jp112sdl/HB-UNI-Sen-WEA/3DDruck/LTB_Weather_Station/images/0f729904a5f2e05334bc5dd88b66ae25_preview_featured.jpg

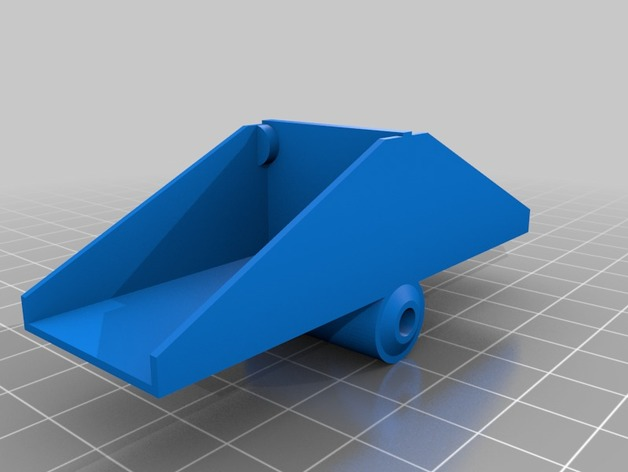
3DDruck/LTB_Weather_Station/images/0f729904a5f2e05334bc5dd88b66ae25_preview_featured.jpg
