jp112sdl/HB-UNI-Sen-WEA/3DDruck/LTB_Weather_Station/images/2f4eb67d5eb4e4a115d83a93fdd548bd_preview_featured.jpg

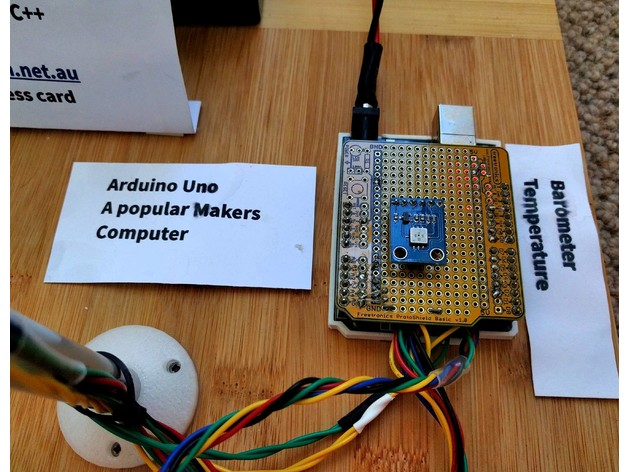
3DDruck/LTB_Weather_Station/images/2f4eb67d5eb4e4a115d83a93fdd548bd_preview_featured.jpg
