jp112sdl/HB-UNI-Sen-WEA/3DDruck/LTB_Weather_Station/images/3d7bd073ae92bd9a4f123ed83592e2da_preview_featured.jpg

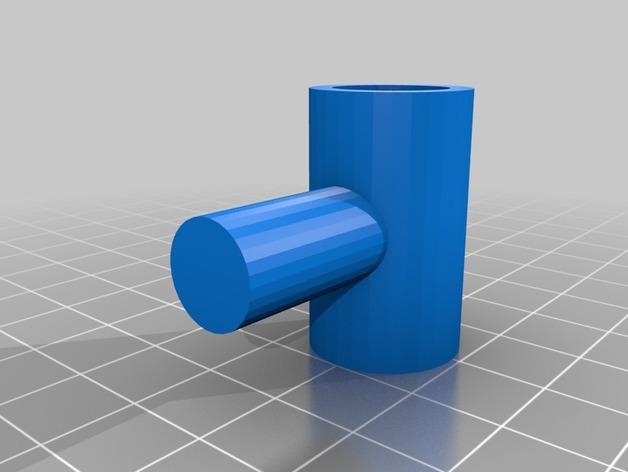
3DDruck/LTB_Weather_Station/images/3d7bd073ae92bd9a4f123ed83592e2da_preview_featured.jpg
