jp112sdl/HB-UNI-Sen-WEA/3DDruck/LTB_Weather_Station/images/6b7efd5bf7d866a3c7be1622005885e2_preview_featured.jpg

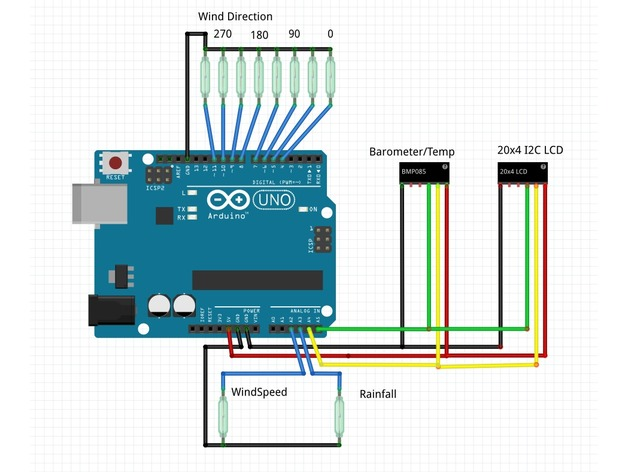
3DDruck/LTB_Weather_Station/images/6b7efd5bf7d866a3c7be1622005885e2_preview_featured.jpg
