jp112sdl/HB-UNI-Sen-WEA/3DDruck/LTB_Weather_Station/images/6f4c261a202a8efb6d09fc4429fcd451_preview_featured.jpg

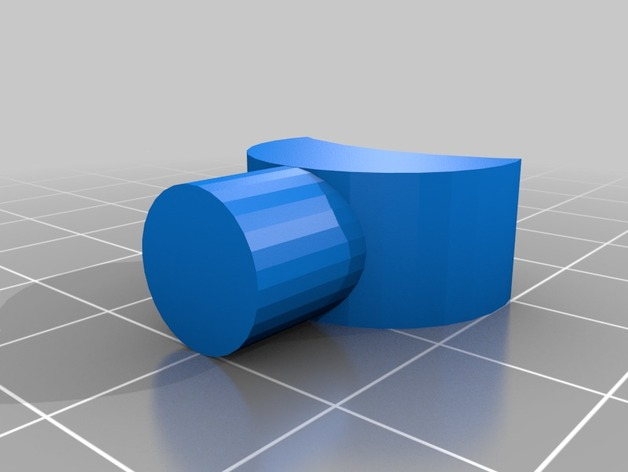
3DDruck/LTB_Weather_Station/images/6f4c261a202a8efb6d09fc4429fcd451_preview_featured.jpg
