jp112sdl/HB-UNI-Sen-WEA/3DDruck/LTB_Weather_Station/images/6f54eee4d5941a1848efe295c70625fb_preview_featured.jpg

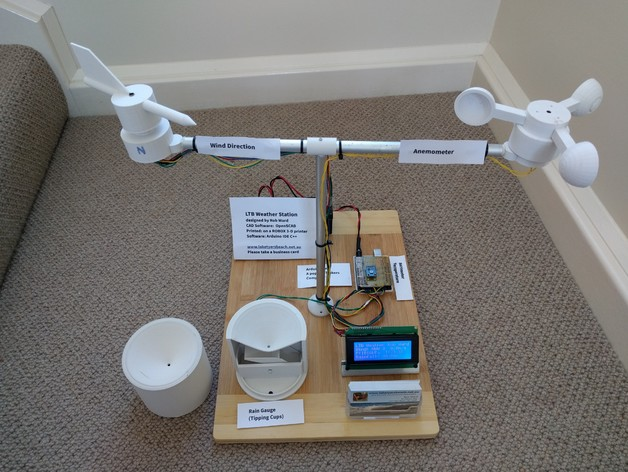
3DDruck/LTB_Weather_Station/images/6f54eee4d5941a1848efe295c70625fb_preview_featured.jpg
