jp112sdl/HB-UNI-Sen-WEA/3DDruck/LTB_Weather_Station/images/7dec8525ebd62560725952abd26e961d_preview_featured.jpg

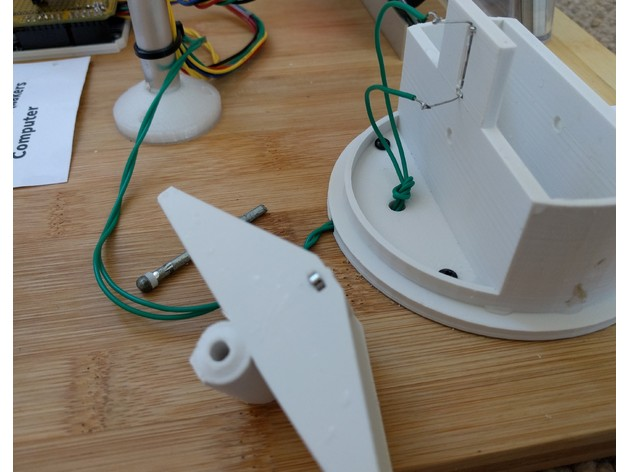
3DDruck/LTB_Weather_Station/images/7dec8525ebd62560725952abd26e961d_preview_featured.jpg
