jp112sdl/HB-UNI-Sen-WEA/3DDruck/LTB_Weather_Station/images/8c24a9ce323ae254777e71005f5087d5_preview_featured.jpg

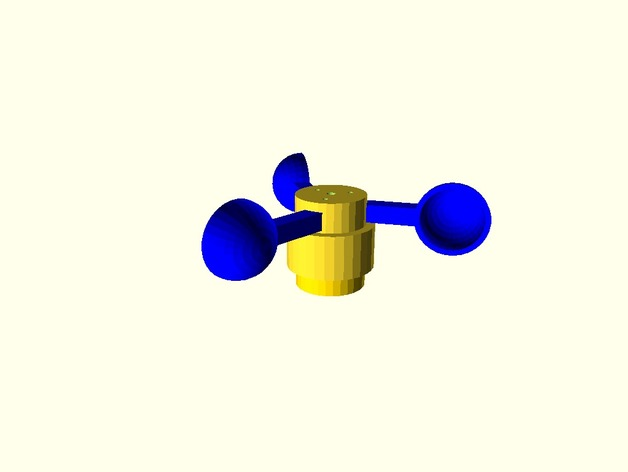
3DDruck/LTB_Weather_Station/images/8c24a9ce323ae254777e71005f5087d5_preview_featured.jpg
