jp112sdl/HB-UNI-Sen-WEA/3DDruck/LTB_Weather_Station/images/45c1245175a171400667a6d880b7b2a3_preview_featured.jpg

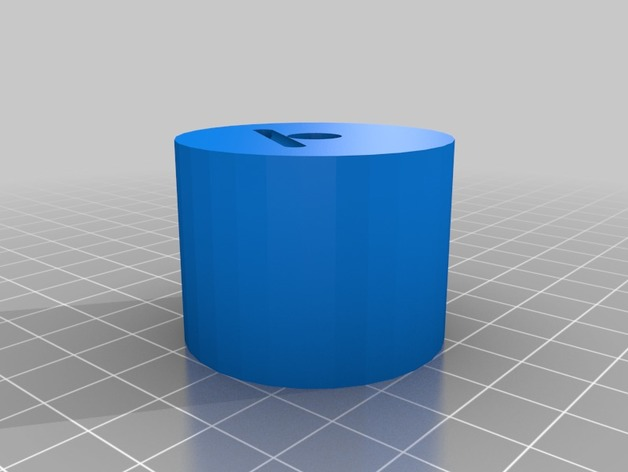
3DDruck/LTB_Weather_Station/images/45c1245175a171400667a6d880b7b2a3_preview_featured.jpg
