jp112sdl/HB-UNI-Sen-WEA/3DDruck/LTB_Weather_Station/images/80a48253a995d0b735cc264a9117a01e_preview_featured.jpg

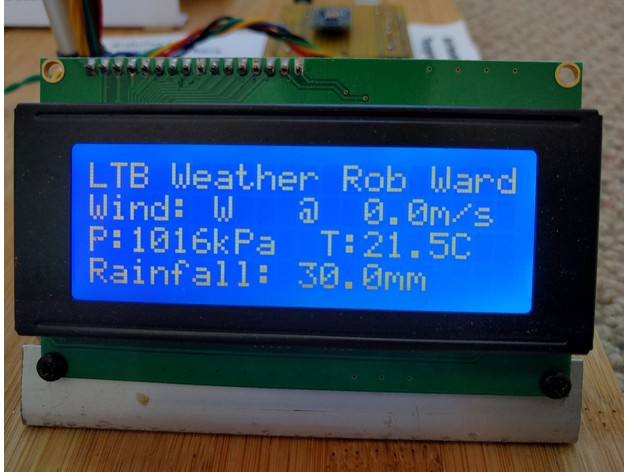
3DDruck/LTB_Weather_Station/images/80a48253a995d0b735cc264a9117a01e_preview_featured.jpg
