jp112sdl/HB-UNI-Sen-WEA/3DDruck/LTB_Weather_Station/images/665cde6034edafd1919697d14e3cbb7f_preview_featured.jpg

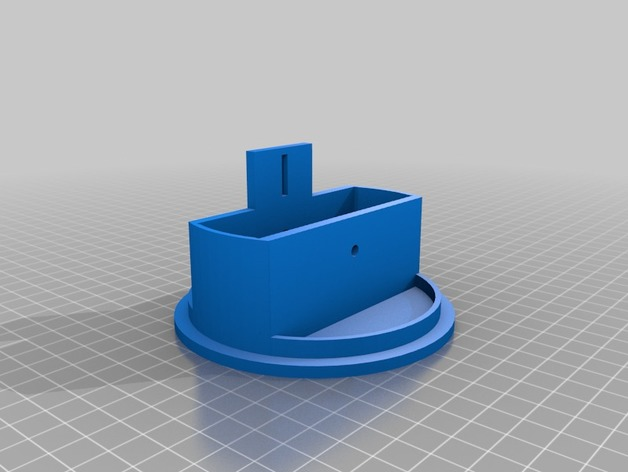
3DDruck/LTB_Weather_Station/images/665cde6034edafd1919697d14e3cbb7f_preview_featured.jpg
