jp112sdl/HB-UNI-Sen-WEA/3DDruck/LTB_Weather_Station/images/4128c8499053c0b8ed6bece59226a6e4_preview_featured.jpg

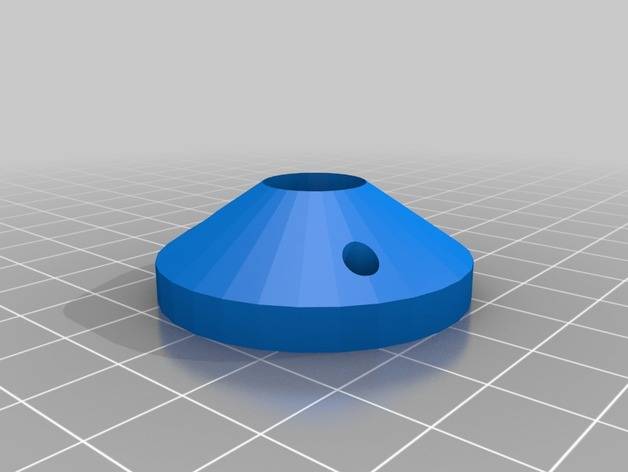
3DDruck/LTB_Weather_Station/images/4128c8499053c0b8ed6bece59226a6e4_preview_featured.jpg
