jp112sdl/HB-UNI-Sen-WEA/3DDruck/LTB_Weather_Station/images/7844c83e0afc9eee98446c4f50ffa83b_preview_featured.jpg

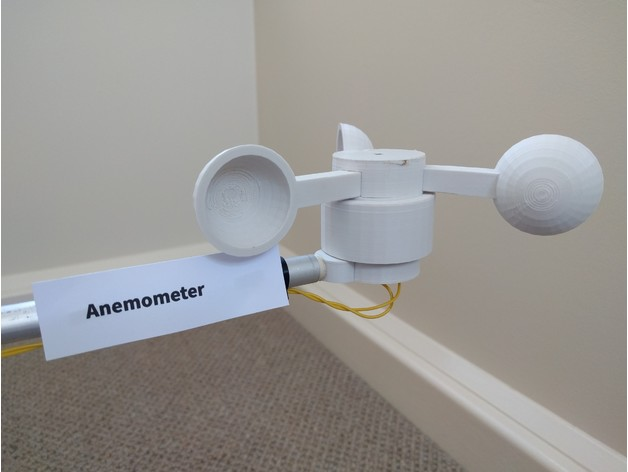
3DDruck/LTB_Weather_Station/images/7844c83e0afc9eee98446c4f50ffa83b_preview_featured.jpg
