jp112sdl/HB-UNI-Sen-WEA/3DDruck/LTB_Weather_Station/images/9245b32cea09aa1bce04a988e750eaf5_preview_featured.jpg

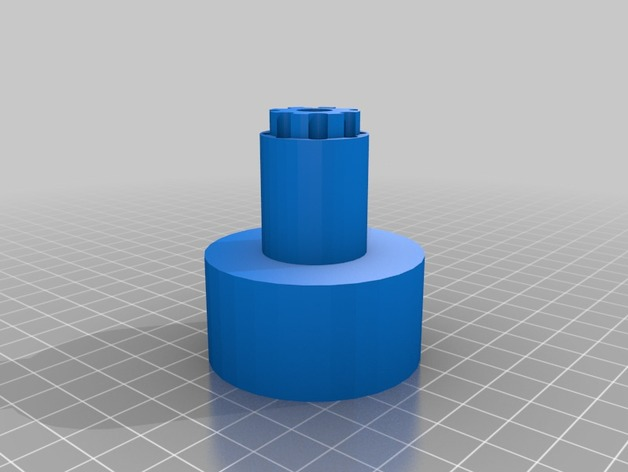
3DDruck/LTB_Weather_Station/images/9245b32cea09aa1bce04a988e750eaf5_preview_featured.jpg
