jp112sdl/HB-UNI-Sen-WEA/3DDruck/LTB_Weather_Station/images/15661ac53241d97e30403f3ccd07a3a0_preview_featured.jpg

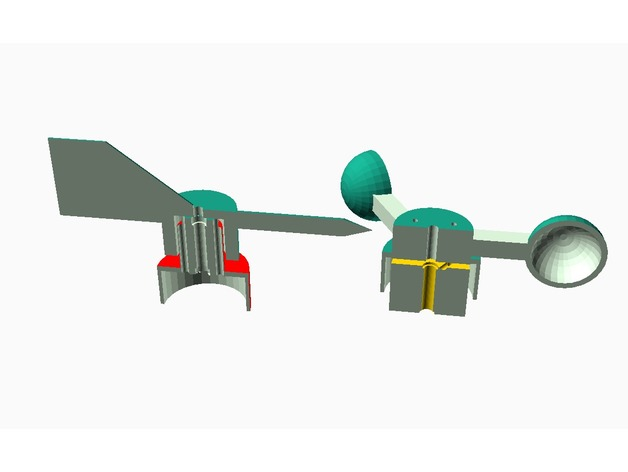
3DDruck/LTB_Weather_Station/images/15661ac53241d97e30403f3ccd07a3a0_preview_featured.jpg
