jp112sdl/HB-UNI-Sen-WEA/3DDruck/LTB_Weather_Station/images/a46b4e9dc1ee91424486a30a58d59f65_preview_featured.jpg

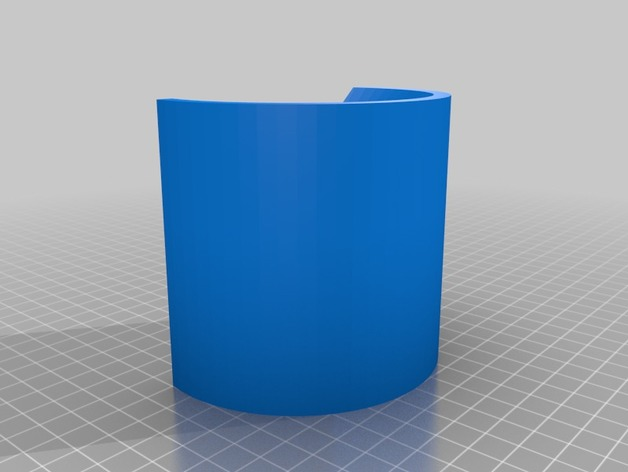
3DDruck/LTB_Weather_Station/images/a46b4e9dc1ee91424486a30a58d59f65_preview_featured.jpg
