jp112sdl/HB-UNI-Sen-WEA/3DDruck/LTB_Weather_Station/images/aa5c15dc5b5677d0f9d4d23d35d61b8d_preview_featured.jpg

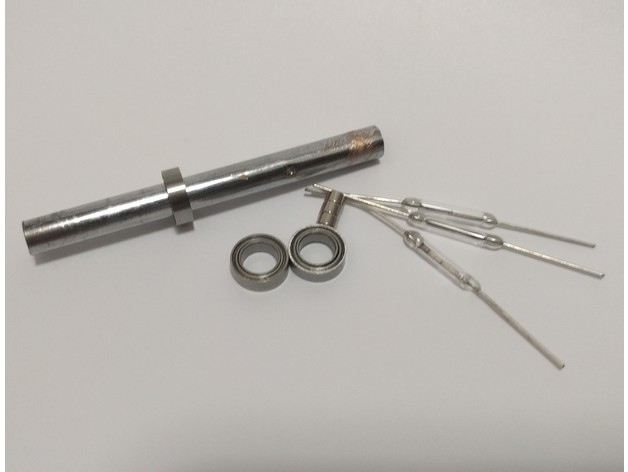
3DDruck/LTB_Weather_Station/images/aa5c15dc5b5677d0f9d4d23d35d61b8d_preview_featured.jpg
