jp112sdl/HB-UNI-Sen-WEA/3DDruck/LTB_Weather_Station/images/abda42896f2a54828468f4c982fa79e0_preview_featured.jpg

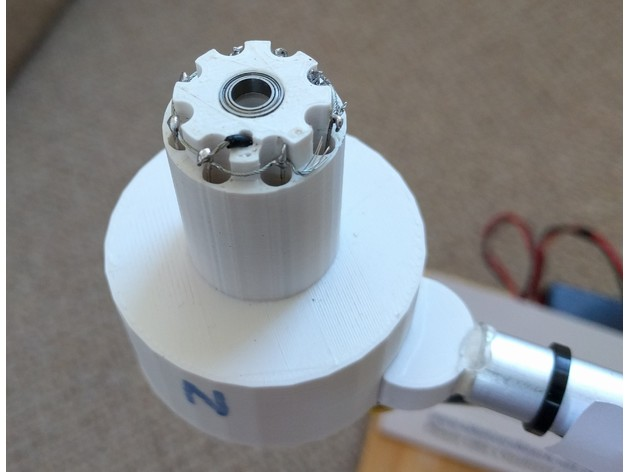
3DDruck/LTB_Weather_Station/images/abda42896f2a54828468f4c982fa79e0_preview_featured.jpg
