jp112sdl/HB-UNI-Sen-WEA/3DDruck/LTB_Weather_Station/images/b8ac2ffeab8d6cb9135d3699e298f246_preview_featured.jpg

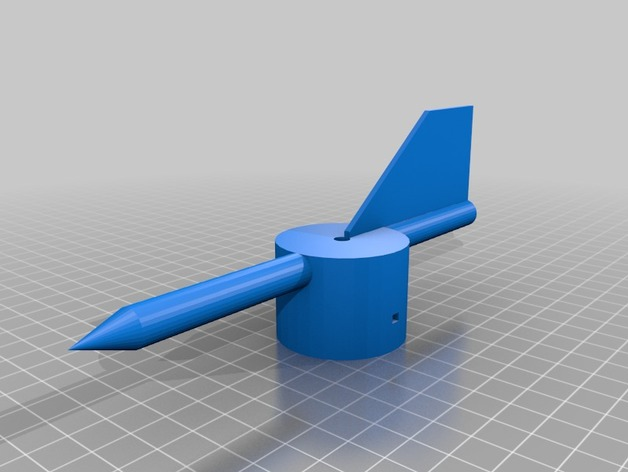
3DDruck/LTB_Weather_Station/images/b8ac2ffeab8d6cb9135d3699e298f246_preview_featured.jpg
