jp112sdl/HB-UNI-Sen-WEA/3DDruck/LTB_Weather_Station/images/c9b82732129711d131ec30678b11e9f1_preview_featured.jpg

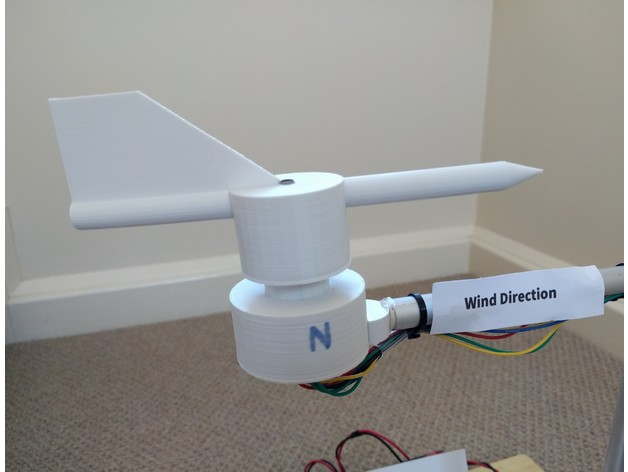
3DDruck/LTB_Weather_Station/images/c9b82732129711d131ec30678b11e9f1_preview_featured.jpg
