jp112sdl/HB-UNI-Sen-WEA/3DDruck/LTB_Weather_Station/images/e383737310d1c1f831bcede16474fa9f_preview_featured.jpg

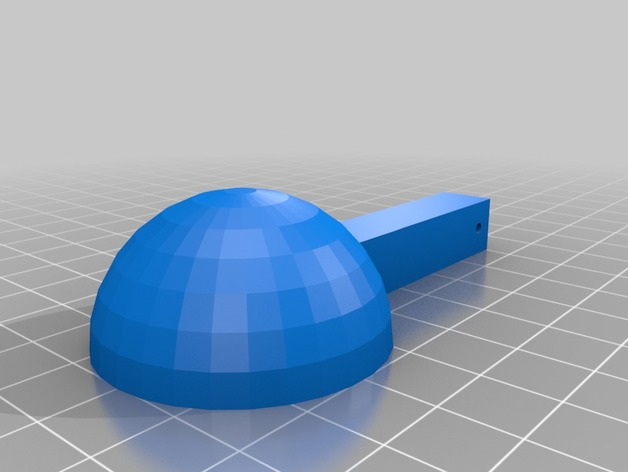
3DDruck/LTB_Weather_Station/images/e383737310d1c1f831bcede16474fa9f_preview_featured.jpg
