jp112sdl/HB-UNI-Sen-WEA/3DDruck/LTB_Weather_Station/images/ef46951516978715a64110eb92978627_preview_featured.jpg

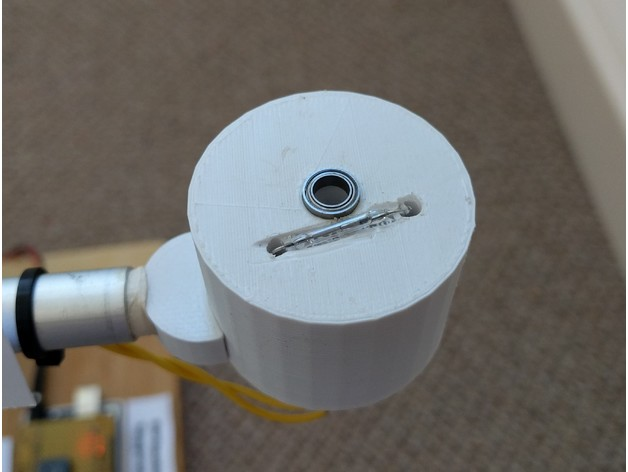
3DDruck/LTB_Weather_Station/images/ef46951516978715a64110eb92978627_preview_featured.jpg
