jp112sdl/HB-UNI-Sen-WEA/3DDruck/LTB_Weather_Station/images/f5733b1c9a6c24a76b0aa705a5f0eb99_preview_featured.jpg

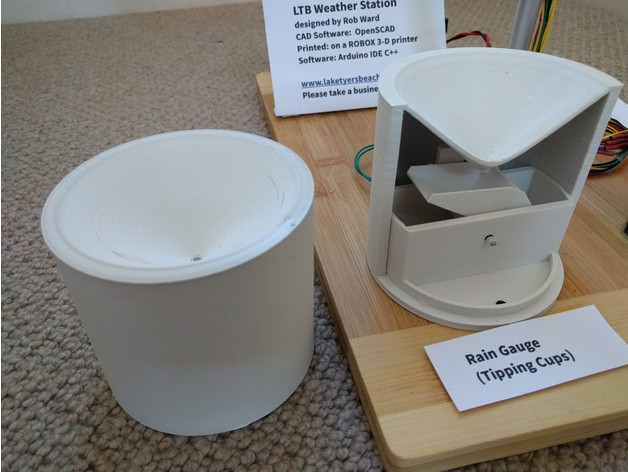
3DDruck/LTB_Weather_Station/images/f5733b1c9a6c24a76b0aa705a5f0eb99_preview_featured.jpg
