jp112sdl/HB-UNI-Sen-WEA/3DDruck/Luftdaten_Stevensson_screen/images/4de7b6a64d3845ae190a4616e7cf8708_preview_featured.jpg

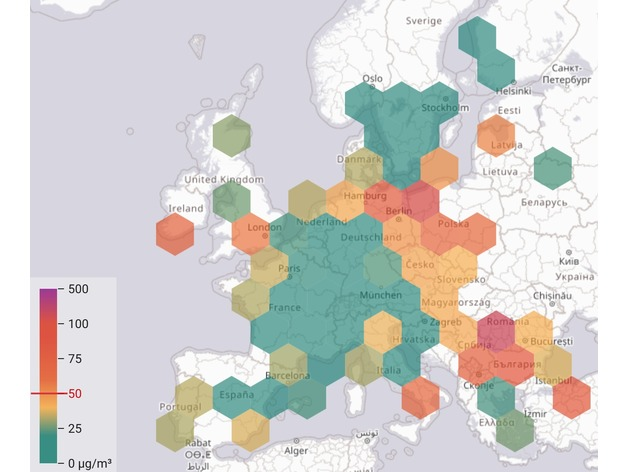
3DDruck/Luftdaten_Stevensson_screen/images/4de7b6a64d3845ae190a4616e7cf8708_preview_featured.jpg
