jp112sdl/HB-UNI-Sen-WEA/3DDruck/Luftdaten_Stevensson_screen/images/44aee935f5d444104dc200fb56da6abe_preview_featured.jpg

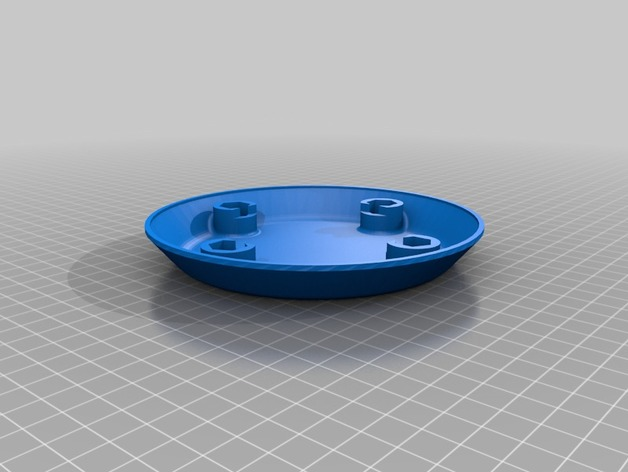
3DDruck/Luftdaten_Stevensson_screen/images/44aee935f5d444104dc200fb56da6abe_preview_featured.jpg
