jp112sdl/HB-UNI-Sen-WEA/3DDruck/Luftdaten_Stevensson_screen/images/160ce06f31e4f0b9b2863523b1d578d7_preview_featured.jpg

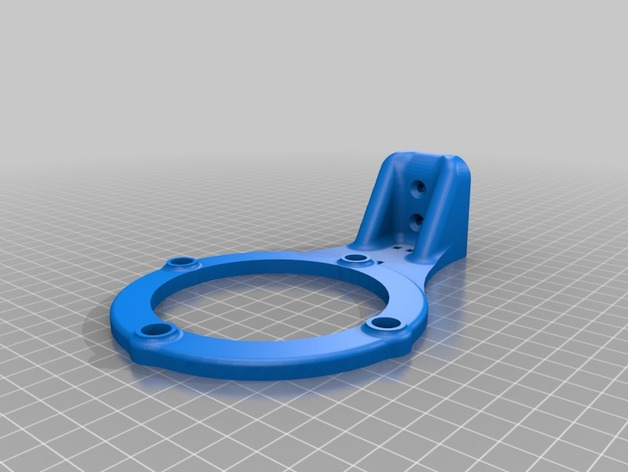
3DDruck/Luftdaten_Stevensson_screen/images/160ce06f31e4f0b9b2863523b1d578d7_preview_featured.jpg
