jp112sdl/HB-UNI-Sen-WEA/3DDruck/Luftdaten_Stevensson_screen/images/da4376fd09404e2d7904c5d9ae312a6a_preview_featured.jpg

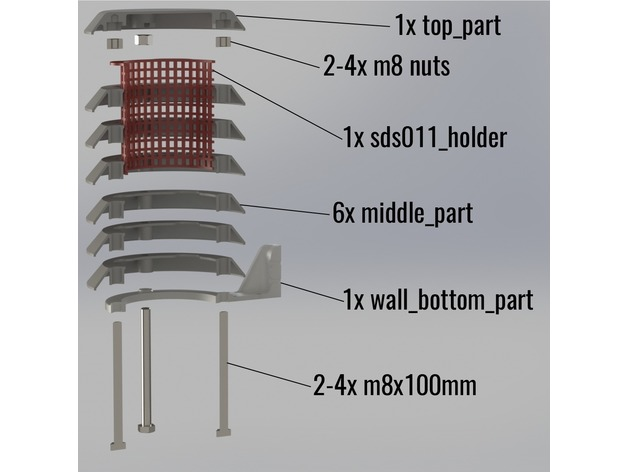
3DDruck/Luftdaten_Stevensson_screen/images/da4376fd09404e2d7904c5d9ae312a6a_preview_featured.jpg
