jp112sdl/HB-UNI-Sen-WEA/Images/0.JPG

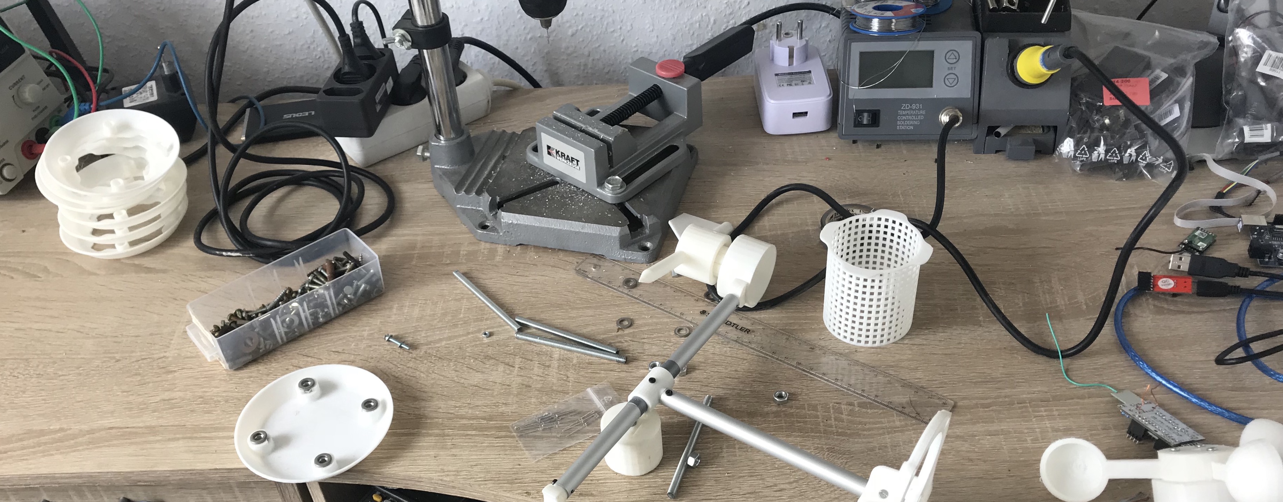
Images/0.JPG
