jp112sdl/HB-UNI-Sen-WEA/Images/1.JPG

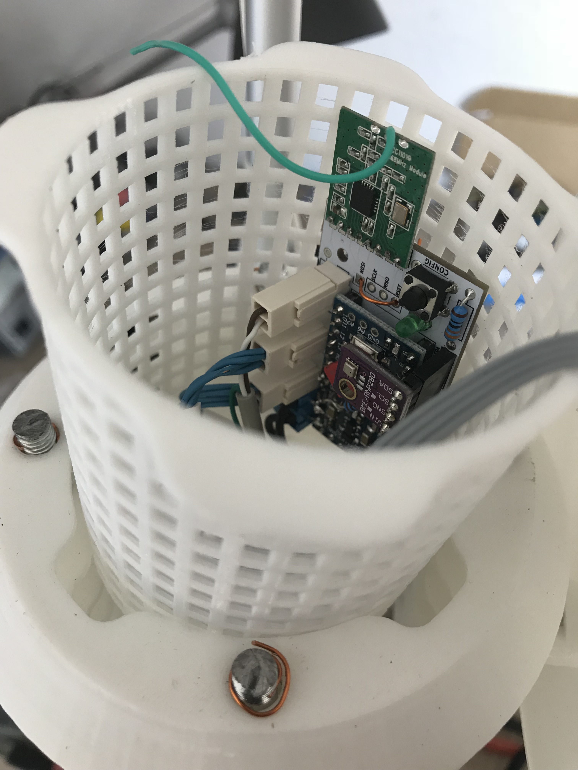
Images/1.JPG
