jp112sdl/HB-UNI-Sen-WEA/Images/2.JPG

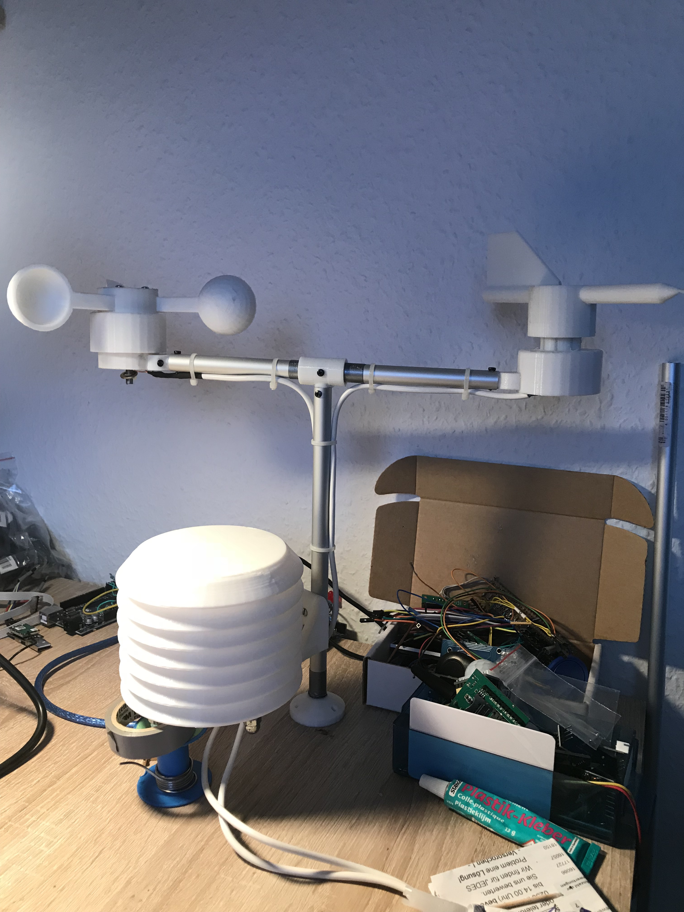
Images/2.JPG
