jp112sdl/HB-UNI-Sen-WEA/Images/3.JPG

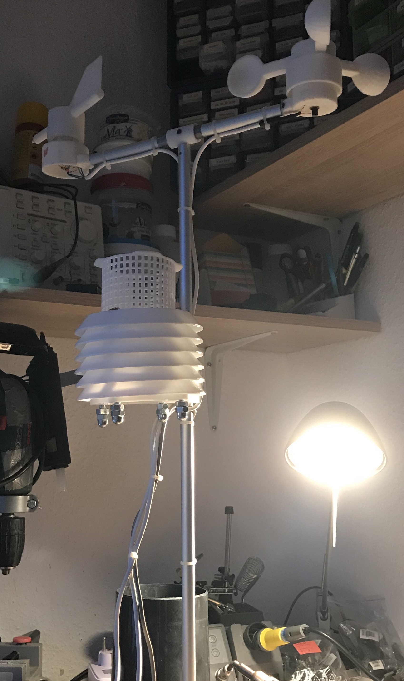
Images/3.JPG
