jp112sdl/HB-UNI-Sen-WEA/Images/Arduino_Boardverwaltung.png

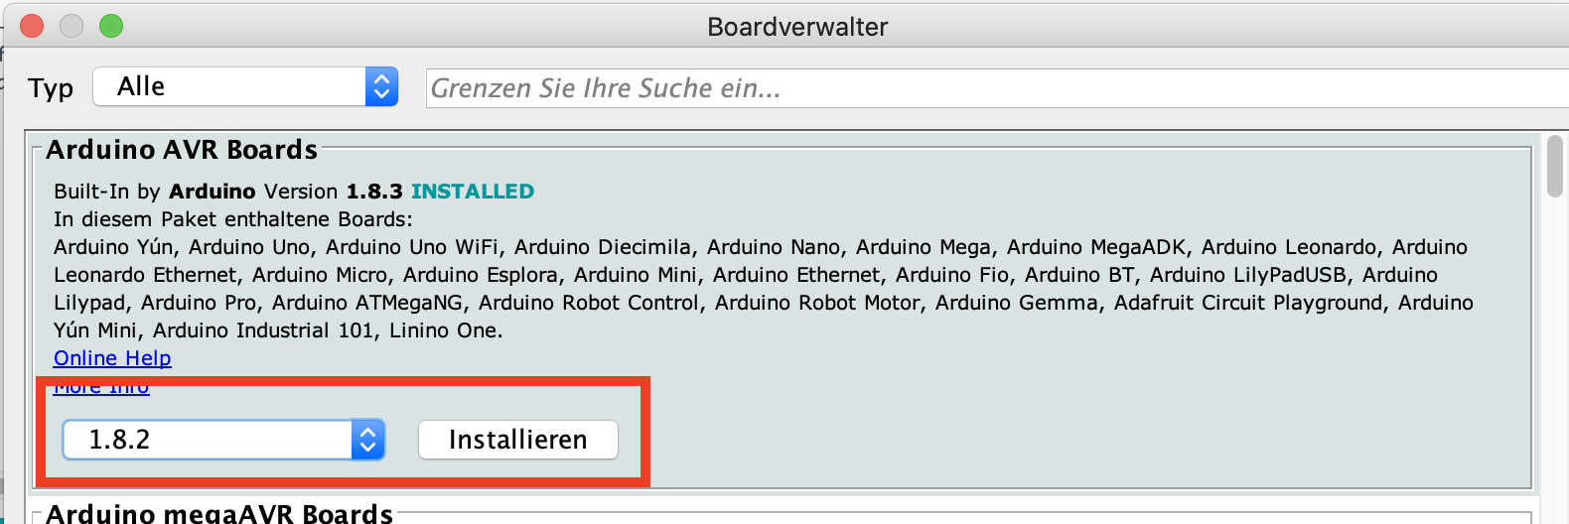
Images/Arduino_Boardverwaltung.png
