jp112sdl/HB-UNI-Sen-WEA/Images/as3935_back_rot.png

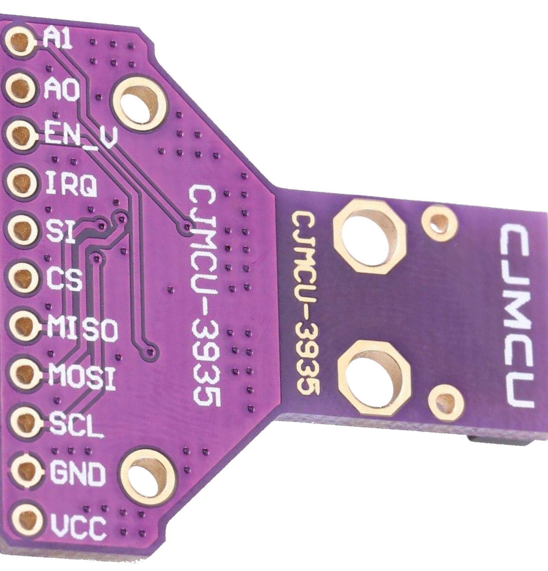
Images/as3935_back_rot.png
