jp112sdl/HB-UNI-Sen-WEA/Images/BME_PFTE.jpeg

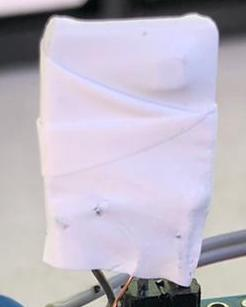
Images/BME_PFTE.jpeg
