jp112sdl/HB-UNI-Sen-WEA/Images/CCU_Addon.png

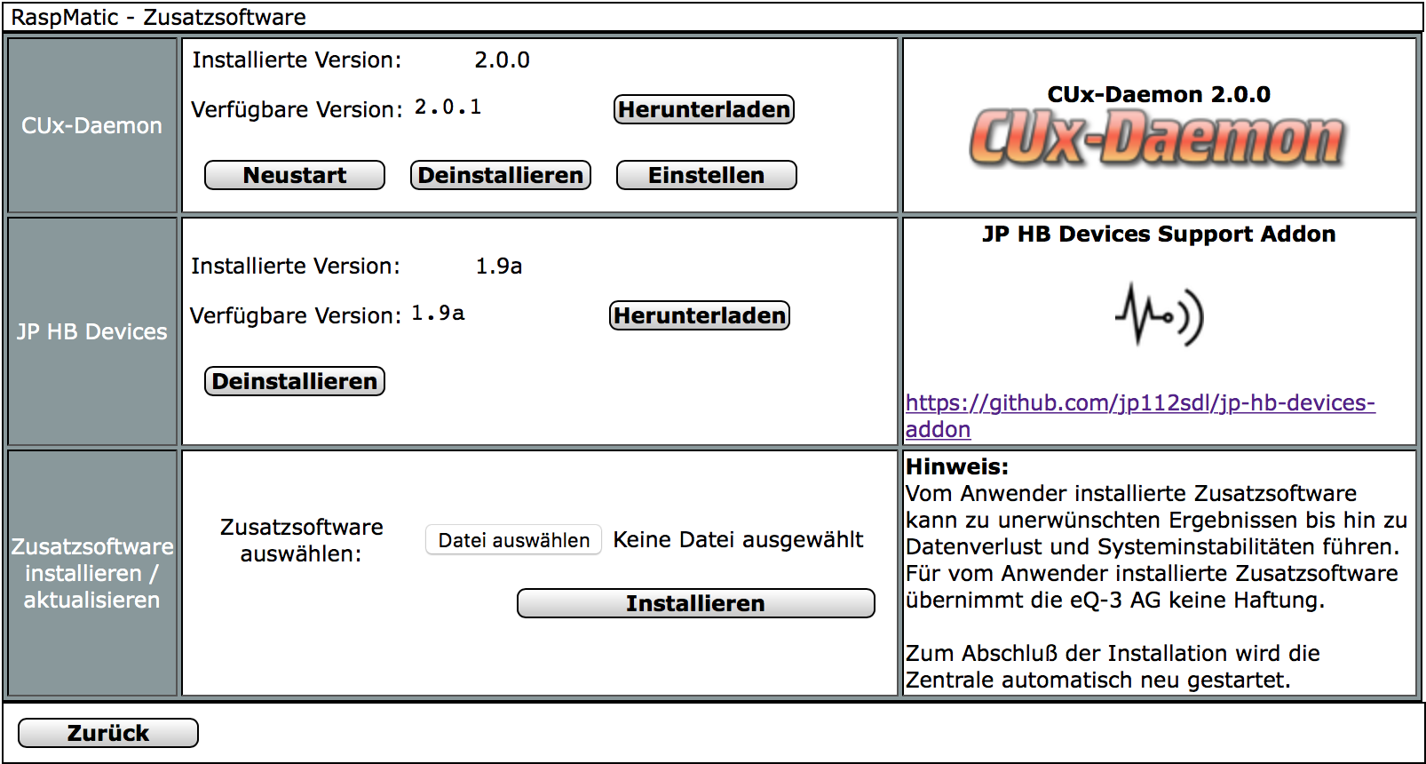
Images/CCU_Addon.png
