jp112sdl/HB-UNI-Sen-WEA/Images/CCU_DV_Regen.png

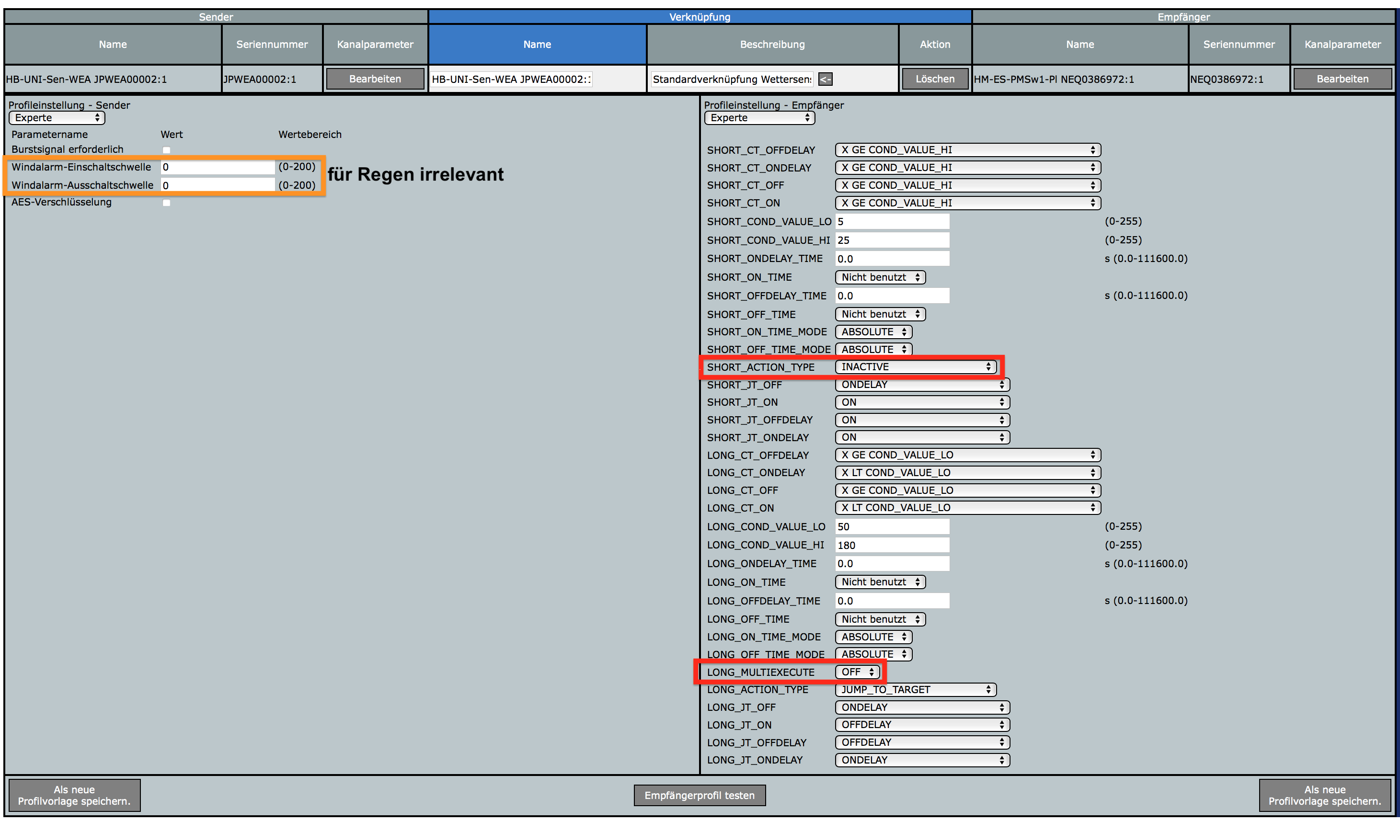
Images/CCU_DV_Regen.png
