jp112sdl/HB-UNI-Sen-WEA/Images/CCU_DV_Sturm.png

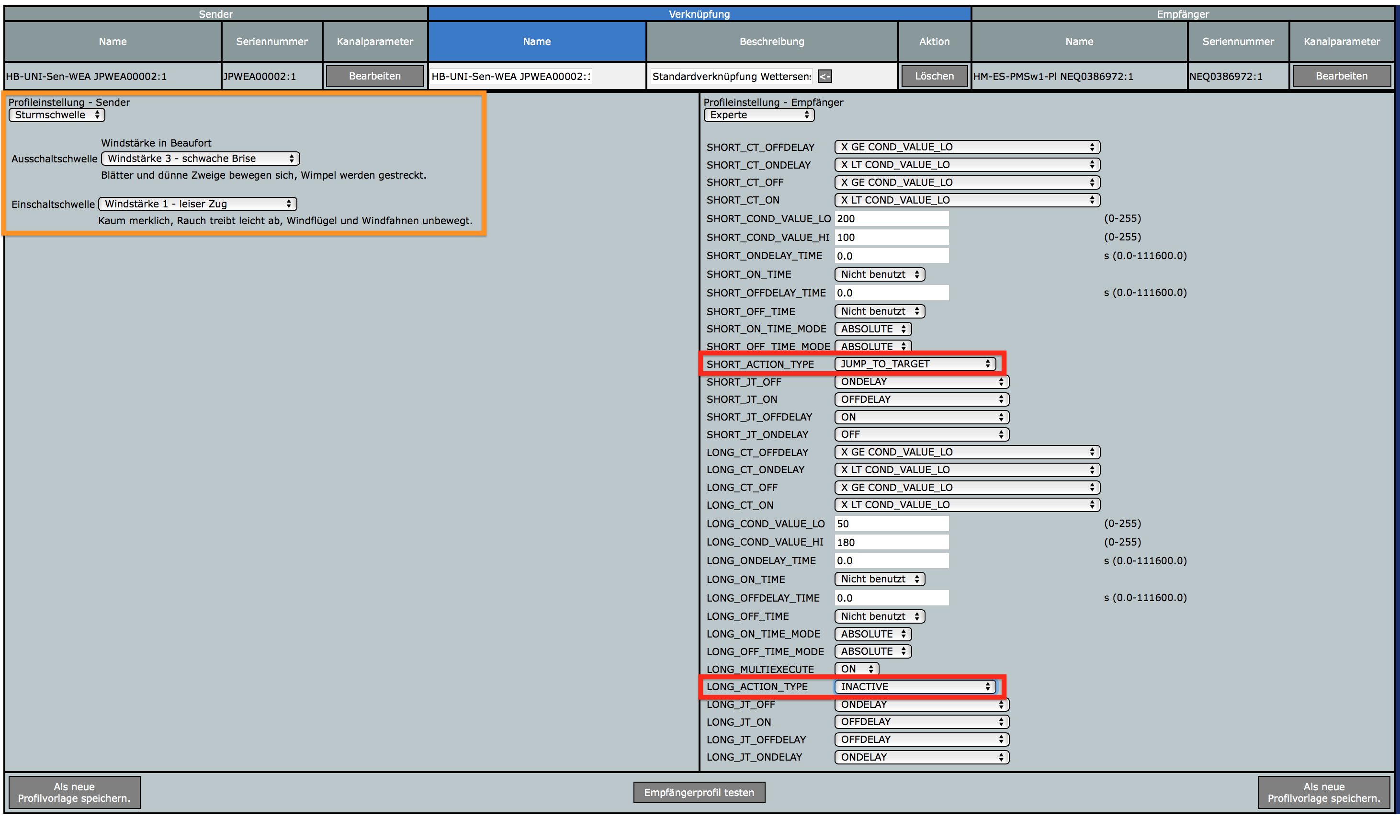
Images/CCU_DV_Sturm.png
