jp112sdl/HB-UNI-Sen-WEA/Images/CCU_Experteneinstellungen.png

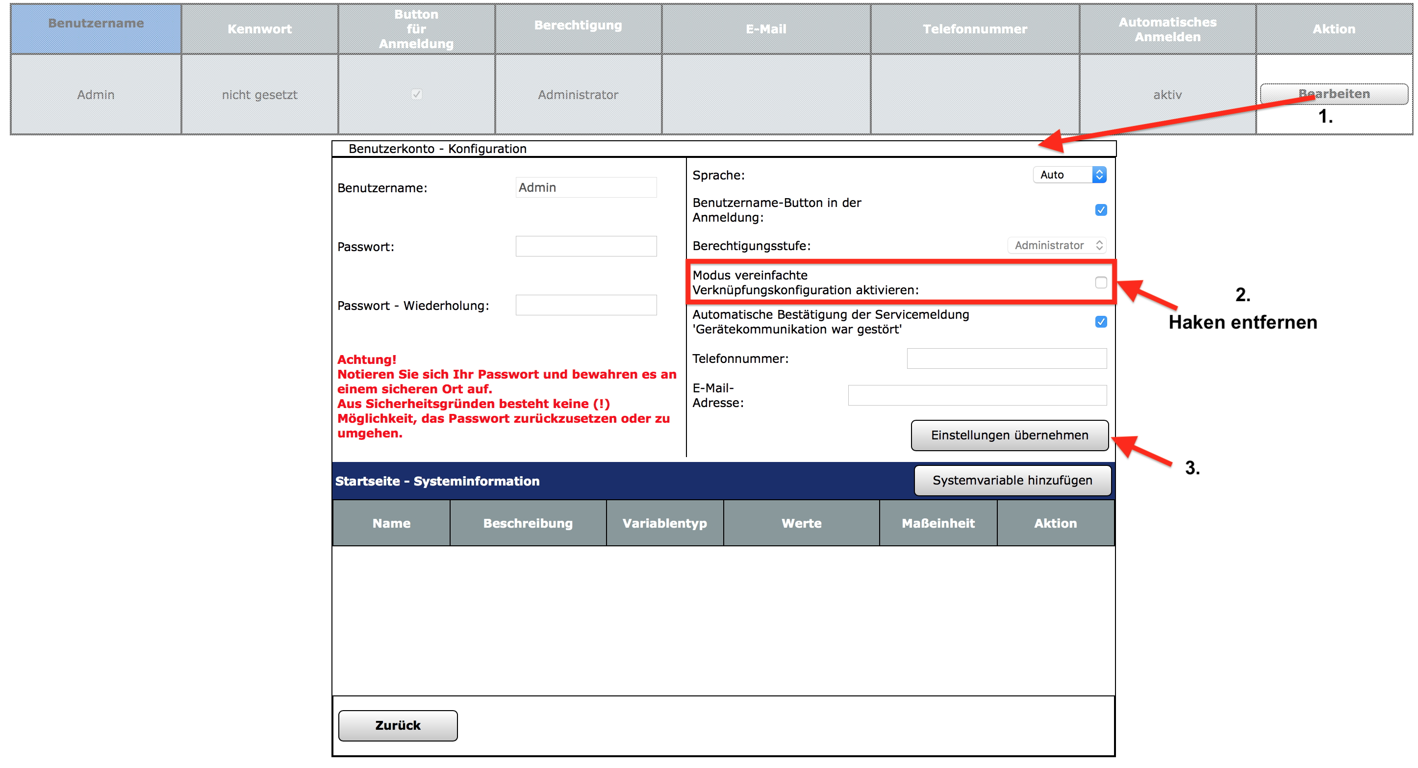
Images/CCU_Experteneinstellungen.png
