jp112sdl/HB-UNI-Sen-WEA/Images/CCU_Geraet.png

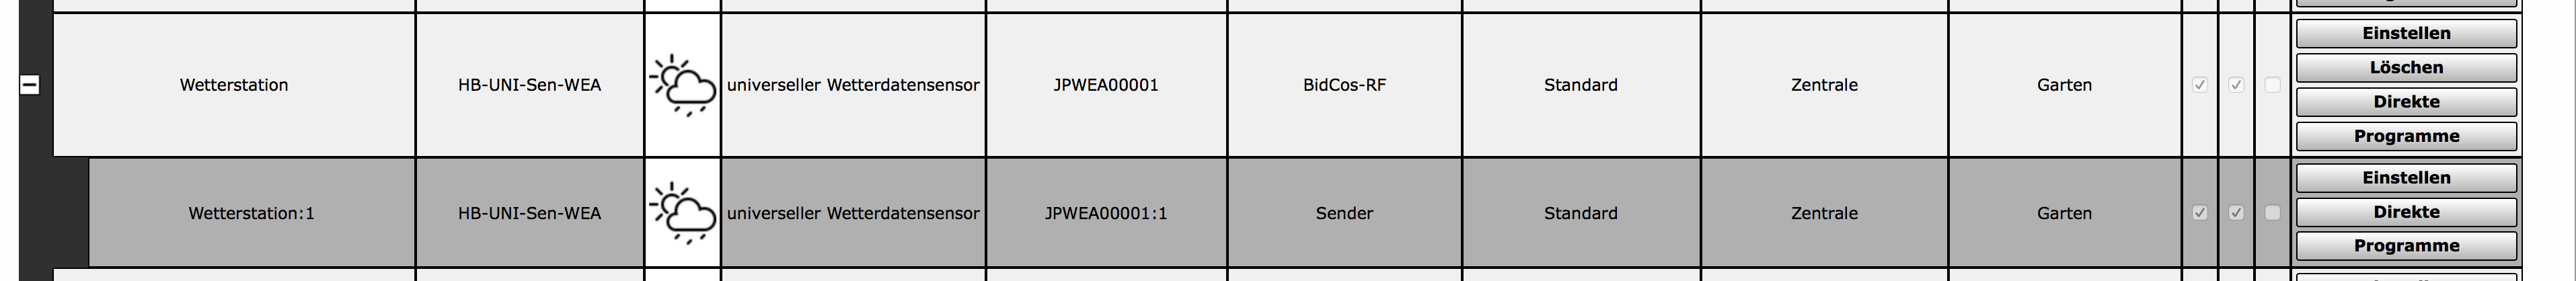
Images/CCU_Geraet.png
