jp112sdl/HB-UNI-Sen-WEA/Images/Connect_AS3935.jpeg

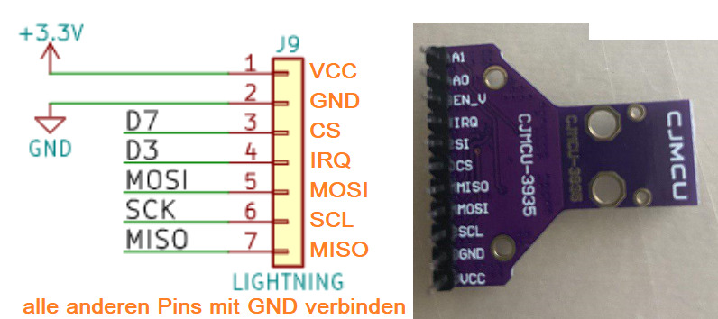
Images/Connect_AS3935.jpeg
