jp112sdl/HB-UNI-Sen-WEA/Images/PCB_Connectors.jpeg

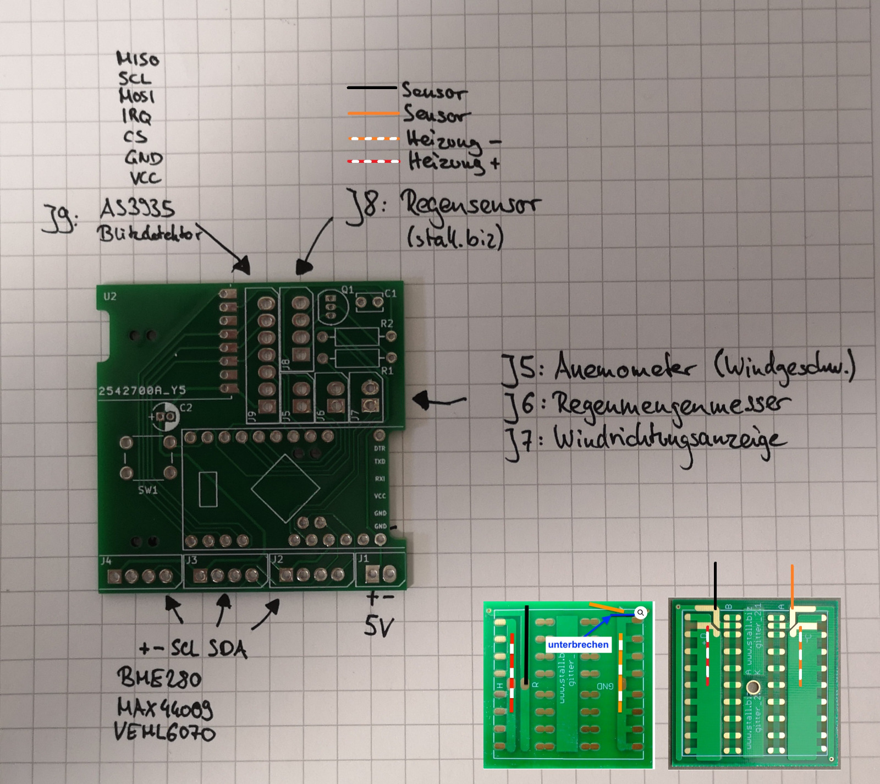
Images/PCB_Connectors.jpeg
