jp112sdl/HB-UNI-Sen-WEA/Images/Platine_bestueckt.jpg

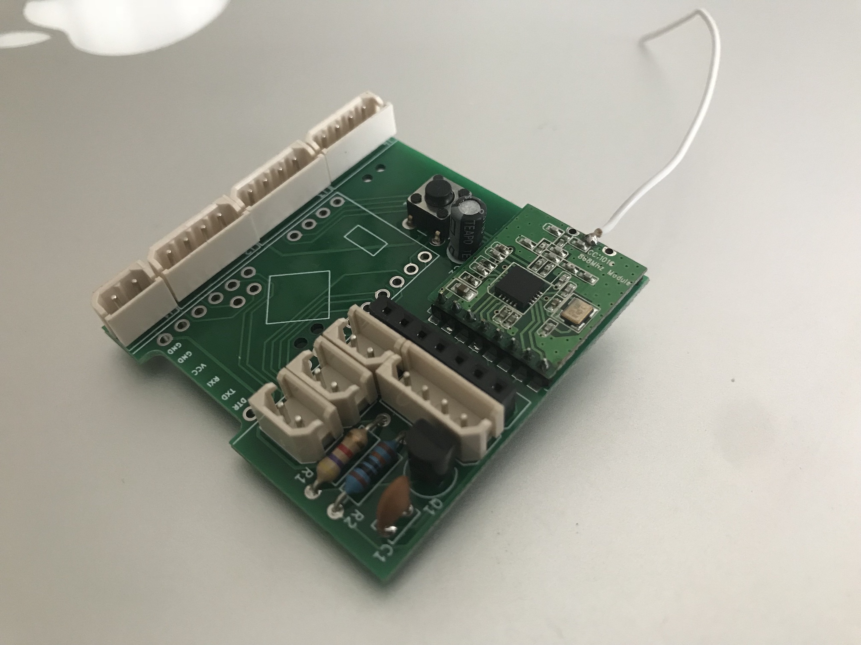
Images/Platine_bestueckt.jpg
