jp112sdl/HB-UNI-Sen-WEA/Images/sample1_2.jpg

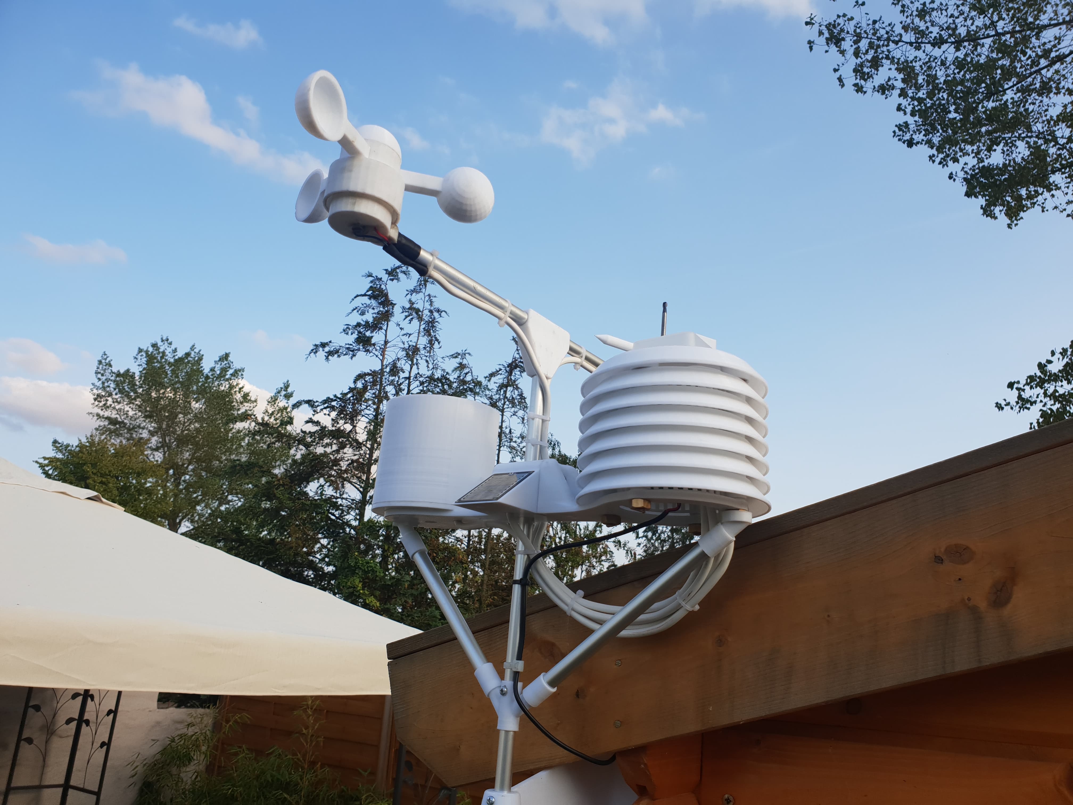
Images/sample1_2.jpg
