jp112sdl/HB-UNI-Sen-WEA/Images/sample1_3.jpg

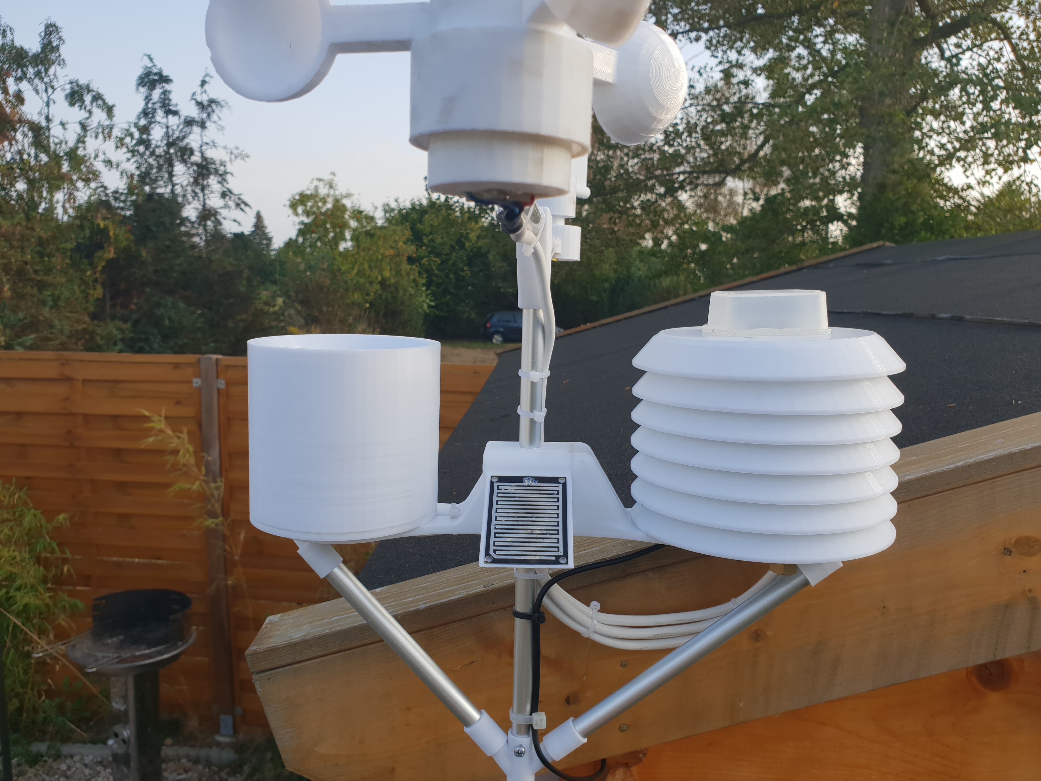
Images/sample1_3.jpg
