jp112sdl/HB-UNI-Sen-WEA/Renkforce_WindVane/2016-11-12-21.50.05.jpg

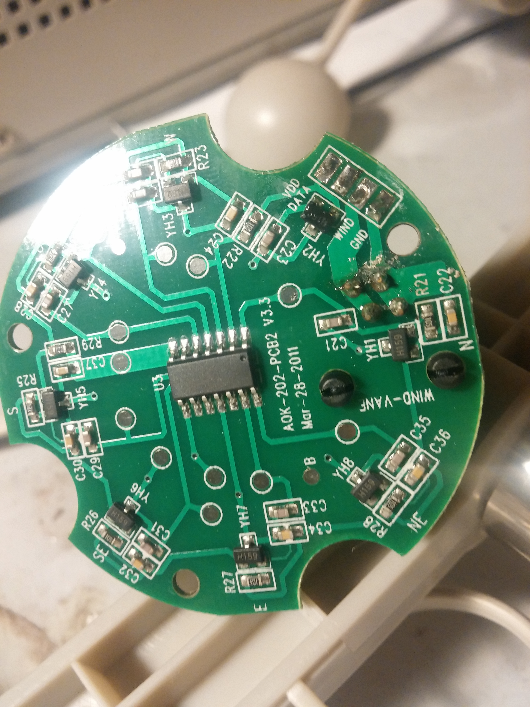
Renkforce_WindVane/2016-11-12-21.50.05.jpg
