jp112sdl/HB-UNI-Sen-WEA/3DDruck/LTB_Weather_Station/files/34Rain_PartFunnel.stl

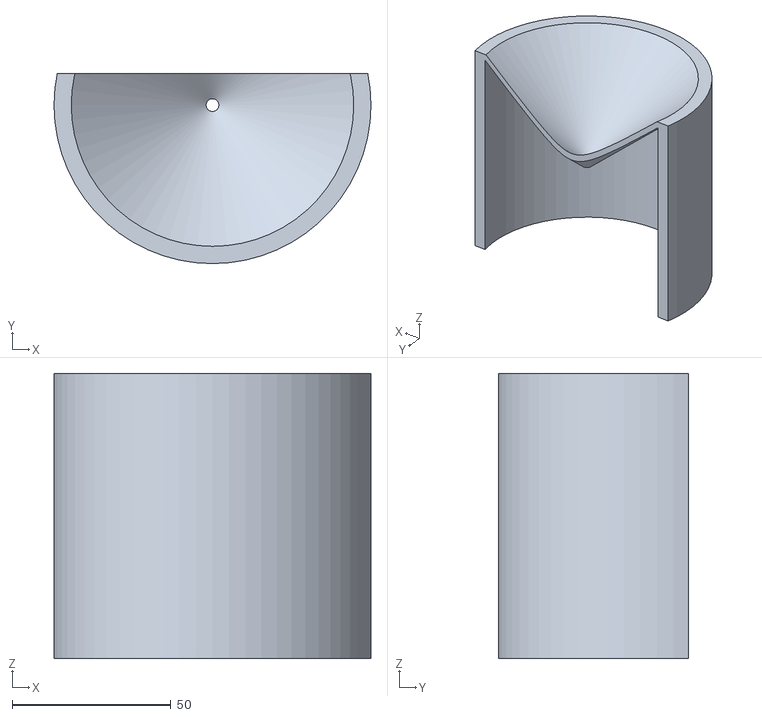
[picture p67: CAD file, 2018-05-30]
3DDruck/LTB_Weather_Station/files/34Rain_PartFunnel.stl
100.0 x 60.0 x 90.0
