jp112sdl/HB-UNI-Sen-WEA/3DDruck/LTB_Weather_Station/files/33Rain_Funnel.stl

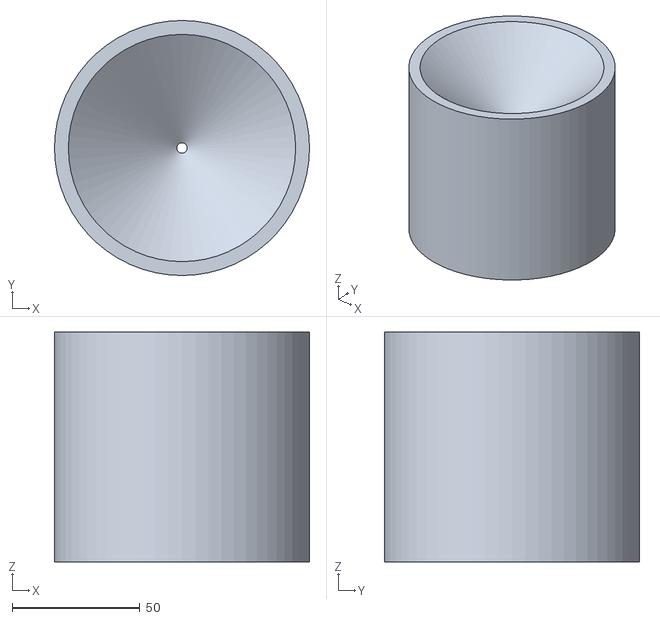
[picture p68: CAD file, 2018-05-30]
3DDruck/LTB_Weather_Station/files/33Rain_Funnel.stl
100.0 x 100.0 x 90.0
