jp112sdl/HB-UNI-Sen-WEA/3DDruck/LTB_Weather_Station/files/04Anem_bracket.stl

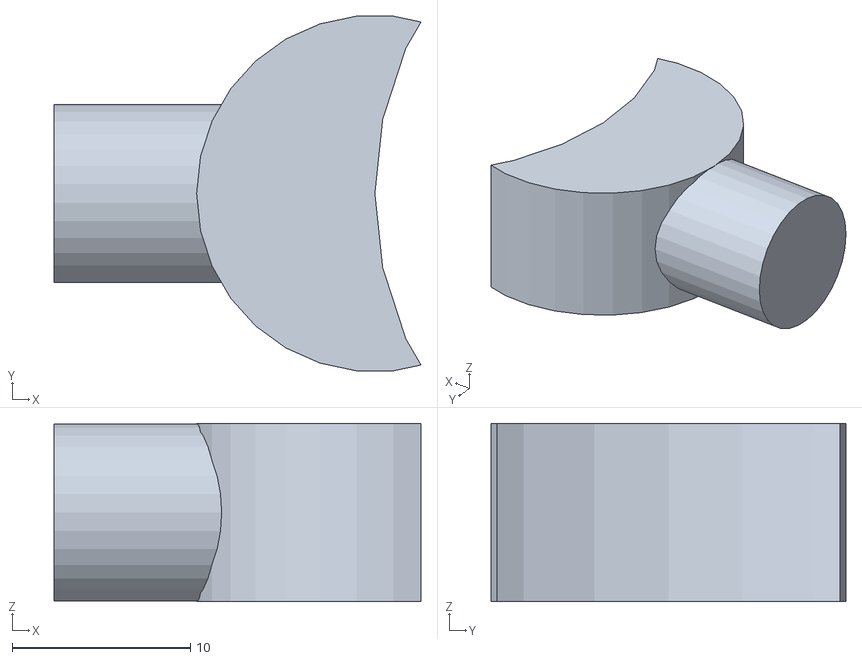
[picture p69: CAD file, 2018-05-30]
3DDruck/LTB_Weather_Station/files/04Anem_bracket.stl
20.6 x 19.9 x 10.0
