jp112sdl/HB-UNI-Sen-WEA/Images/wiring.png

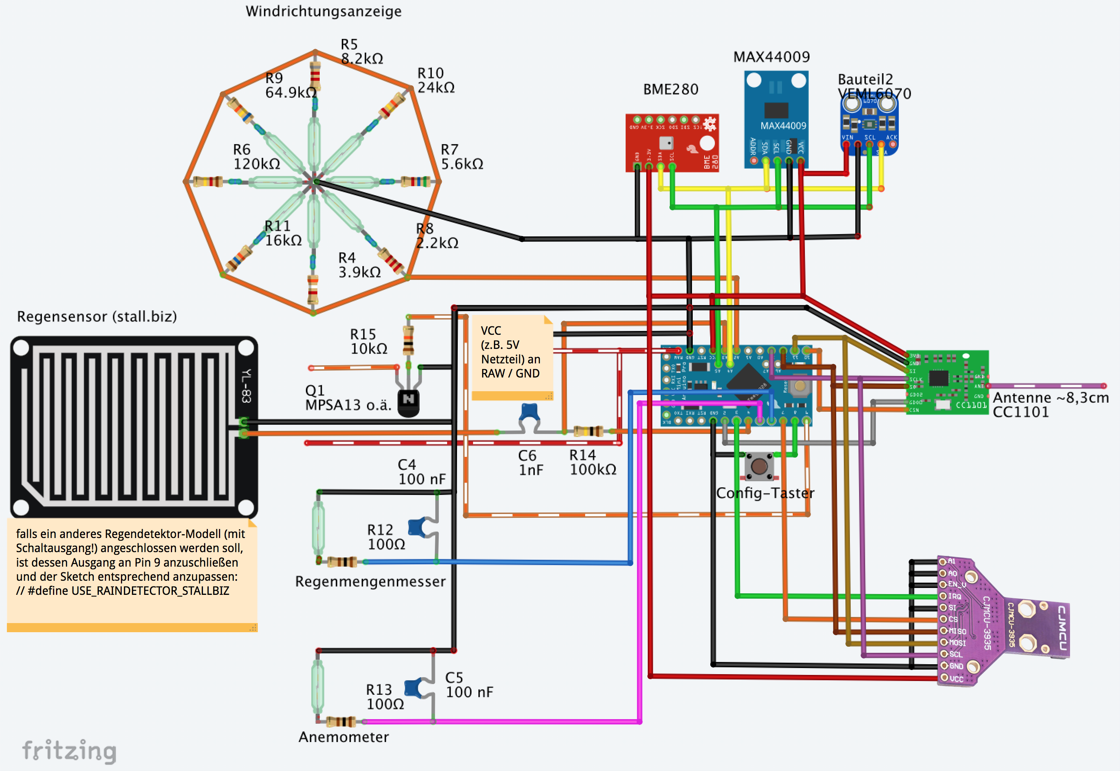
Images/wiring.png
