jp112sdl/HB-UNI-Sen-WEA/PWFusion_AS3935_I2C.h

#ifndef PWF_AS3935_I2C_h
#define PWF_AS3935_I2C_h

#include "Arduino.h"
#include "avr/pgmspace.h"
#include "util/delay.h"
#include "stdlib.h"
#include "I2C.h"

class PWF_AS3935_I2C
{
 public:
	PWF_AS3935_I2C(uint8_t DEVADDx, uint8_t IRQx);
	void AS3935_ManualCal(uint8_t capacitance, uint8_t location, uint8_t disturber);
	void AS3935_Reset(void);
	void AS3935_PowerUp(void);
	void AS3935_PowerDown(void);
	void AS3935_DisturberEn(void);
	void AS3935_DisturberDis(void);
	void AS3935_SetIRQ_Output_Source(uint8_t irq_select);
	void AS3935_SetTuningCaps(uint8_t cap_val);
	uint8_t AS3935_GetInterruptSrc(void);
	uint8_t AS3935_GetLightningDistKm(void);
	uint32_t AS3935_GetStrikeEnergyRaw(void);
	uint8_t AS3935_SetMinStrikes(uint8_t min_strk);
	void AS3935_ClearStatistics(void);
	void AS3935_SetIndoors(void);
	void AS3935_SetOutdoors(void);
	uint8_t AS3935_GetNoiseFloorLvl(void);
	void AS3935_SetNoiseFloorLvl(uint8_t nf_sel);
	uint8_t AS3935_GetWatchdogThreshold(void);
	void AS3935_SetWatchdogThreshold(uint8_t wdth);
	uint8_t AS3935_GetSpikeRejection(void);
	void AS3935_SetSpikeRejection(uint8_t srej);
	void AS3935_SetLCO_FDIV(uint8_t fdiv);
	void AS3935_PrintAllRegs(void);
	
 private:
	uint8_t _irq, _devadd;
	uint8_t _sing_reg_read(uint8_t RegAdd);
	void _sing_reg_write(uint8_t RegAdd, uint8_t DataMask, uint8_t RegData);
	void _AS3935_Reset(void);
	void _CalRCO(void);
};

#endif
